essele/Fluke_Z8_Emulator/PSoC_Workspace/Fluke Z8 Emulator.cydsn/firmware_8840A_v23.c

/* ========================================
 *
 * Copyright YOUR COMPANY, THE YEAR
 * All Rights Reserved
 * UNPUBLISHED, LICENSED SOFTWARE.
 *
 * CONFIDENTIAL AND PROPRIETARY INFORMATION
 * WHICH IS THE PROPERTY OF your company.
 *
 * ========================================
*/

#include "project.h"


uint8_t             code[8192] = {
        0x00, 0x00, 0x03, 0xe2, 0x00, 0x80, 0x07, 0x7a, 0x00, 0x00, 0x00, 0xd7, 0x8f, 0x31, 0xf0, 0xbc, 
		0x00, 0x9f, 0x9c, 0x31, 0xac, 0x10, 0x7c, 0xc9, 0xe6, 0x03, 0x20, 0xfc, 0x80, 0x4c, 0x01, 0x5c, 
		0x05, 0x1c, 0x83, 0x6c, 0xfb, 0x76, 0x02, 0x80, 0x6d, 0x0e, 0xf2, 0x6c, 0x0b, 0xd6, 0x0e, 0x39, 
		0x8d, 0x1b, 0xd5, 0x9f, 0xd6, 0x07, 0xa7, 0x8f, 0x76, 0x4d, 0x04, 0x6b, 0x0e, 0x76, 0x02, 0x02, 
		0xeb, 0x09, 0x56, 0xfb, 0xfb, 0x9f, 0xd6, 0x04, 0xfb, 0x8b, 0xe8, 0x46, 0xfb, 0x04, 0x9f, 0x76, 
		0x4f, 0x08, 0x6b, 0x08, 0x76, 0x4f, 0x80, 0xeb, 0x03, 0xd6, 0x0e, 0x1d, 0x76, 0x03, 0x04, 0xeb, 
		0x0e, 0x76, 0x4f, 0x04, 0xeb, 0xcd, 0x8f, 0xd6, 0x0e, 0x39, 0xd6, 0x11, 0xec, 0x8b, 0x0c, 0x76, 
		0x4f, 0x04, 0x6b, 0xbf, 0x8f, 0xd6, 0x0e, 0x39, 0xd6, 0x12, 0x1f, 0xd6, 0x0e, 0x49, 0x8b, 0xb3, 
		0xd6, 0x0e, 0x39, 0x8d, 0x10, 0x00, 0xd6, 0x1b, 0x23, 0xd6, 0x1b, 0x95, 0xd6, 0x0e, 0x49, 0x56, 
		0x4f, 0x7f, 0x76, 0xfe, 0x10, 0x6b, 0x06, 0xd6, 0x05, 0x04, 0x56, 0xfe, 0xef, 0x24, 0x34, 0xed, 
		0x34, 0x33, 0xec, 0x34, 0x32, 0xeb, 0x70, 0x38, 0xb0, 0x26, 0xd6, 0x0e, 0x63, 0x50, 0x38, 0xb8, 
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
		0x0e, 0x8f, 0x46, 0xfb, 0x20, 0x56, 0xfa, 0xdf, 0x56, 0xf1, 0x7f, 0x46, 0xf1, 0x08, 0x9f, 0x76, 
		0x08, 0x80, 0x6b, 0x06, 0x46, 0x08, 0xc0, 0xd6, 0x0e, 0x5d, 0xb0, 0xee, 0xb0, 0xef, 0xb0, 0x20, 
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
};

/* [] END OF FILE */
